squeedee/daisy-studio/sim/input/.!55486!Input-sim.asc

C5: cap
R11: res; 11k
R12: res; 1k
V_neg: voltage; 12
V_pos: voltage; 12
Named nets: +12V, 0, -12V, n+, n-, V_COM, IN_after_rcvr, Opamp_Out, Seed_In, Codec, IN_after_rcvr_Hot, Opamp_Out_Hot, Seed_In_Hot, n+_Hot, n-_Hot, Codec_Hot
