squeedee/daisy-studio/sim/input/amp-atten-bjt-tolerance.asc

C1: cap; 4.7µ
C2: cap; 20pF
C5: cap; {pcref}
C6: cap; {ncref}
C_aa: cap; 1n
D1: diode; RED_LED
Q1: pnp; 2N3906
Q2: npn; 2N3904
R1: res; {r1}
R2: res; {r2}
R3: res; 3k3
R4: res; 3k6
R5: res; 10k
R11: res; {pr1}
R12: res; {pr2}
R13: res; {nr2}
R14: res; {nr1}
R_led: res; 1k
R_pb: Res; {rpb}
R_pt: Res; {rpt}
U1: UniversalOpAmp2; Avol=1Meg GBW=53Meg Slew=24Meg Vhigh={vhi} Vlow={vlo}
U2: UniversalOpAmp2
V1: voltage; SINE(0 {vin} 1000); AC 1
V_COM: voltage; 2.5
V_neg: voltage; {v_rail}
V_pos: voltage; {v_rail}
V_thresh: voltage; 1
Named nets: +12V, 0, -12V, n+, n-, V_COM, IN_after_rcvr, Seed_In, Codec, Wiper
; settle for 3 seconds, 100ms of samples
.tran 0 3 2.9 1u
.model 2N3904 NPN(IS=6.734f BF=416.4 NF=1.259 VAF=74.03 IKF=66.78m ISE=6.734f NE=1.259 BR=0.7389 NR=2 VAR=28 IKR=0 ISC=0 NC=2 RB=10 RC=1 CJE=3.638p VJE=0.65 MJE=0.3085 TF=301.2p CJC=4.493p VJC=0.3742 MJC=0.2957 FC=0.5 TR=239.5n)
.model 2N3906 PNP(IS=1.41f BF=172.1 NF=1.232 VAF=115.7 IKF=30m ISE=1.41f NE=1.232 BR=3.72 NR=1.5 VAR=28 IKR=0 ISC=0 NC=2 RB=10 RC=1 CJE=4.5p VJE=0.65 MJE=0.28 TF=600p CJC=3.4p VJC=0.65 MJC=0.26 FC=0.5 TR=48n)
.model RED_LED D(IS=9.6e-18 N=2 RS=5.6 BV=5 IBV=10u EG=1.95)
Signal level after THAT 1246 (-6dB); 8.68V amp = +24 dBu balanced peak
BJT Clamp (2N3906/2N3904, ref dividers)
;Tolerance sweep: 5 corners x 3 testcases = 15 runs
;corner 1=TYP, 2=OPA_CLIP (max gain, min rails)
;        3=CLAMP_TIGHT (min V_ref, min rails)
;        4=CLAMP_LOOSE (max V_ref, max rails)
;        5=GAIN_LOW (min gain)
;testcase 1=+4dBu pk=1.0  (nominal pro, max pot)
;         2=+24dBu pk=0.26 (hot signal, full-scale)
;         3=+24dBu pk=1.0  (hot signal, mis-set)
Seed L/R In
PCM3060 Load
Clamp Ref Dividers (10k/1.6k from +/-12V, 47uF)
.param corner=1
.param testcase=1
.param v_rail=table(corner,1,12,2,11.4,3,11.4,4,12.6,5,12)
.param vhi=v_rail-1
.param vlo=1-v_rail
.param r1=table(corner,1,10k,2,9.9k,3,10k,4,10k,5,10.1k)
.param r2=table(corner,1,12k,2,12.12k,3,12k,4,12k,5,11.88k)
.param pr1=table(corner,1,10k,2,10k,3,10.1k,4,9.9k,5,10k)
.param pr2=table(corner,1,1.5k,2,1.5k,3,1.485k,4,1.515k,5,1.5k)
.param nr1=table(corner,1,10k,2,10k,3,10.1k,4,9.9k,5,10k)
.param nr2=table(corner,1,1.5k,2,1.5k,3,1.485k,4,1.515k,5,1.5k)
.param pcref=47u
.param ncref=47u
.param pk=table(testcase,1,1.0,2,0.26,3,1.0)
.param vin=table(testcase,1,0.868,2,8.68,3,8.68)
.param rpt={10k*(1-pk)+1m}
.param rpb={10k*pk+1m}
.step param corner list 1 2 3 4 5
.step param testcase list 1 2 3
.four 1000 V(Codec)
.meas tran codec_pp pp V(Codec)
.meas tran codec_max max V(Codec)
.meas tran codec_min min V(Codec)
.meas tran seed_pp pp V(Seed_In)
.meas tran seed_max max V(Seed_In)
.meas tran seed_min min V(Seed_In)
Clip indicator comparator
V_thresh sets trip point: 1V threshold on Seed_In (trim pot range AGND to n+)
Input level pot (10k log, 3-term divider)
;R_pt = top half, R_pb = bottom half
;pk = wiper position (0=mute, 1=CW max)
C_aa anti-alias 1nF C0G
;forms LPF with R_out + wiper Z
