squeedee/daisy-studio/sim/input/thd-plus4db.asc

C1: cap; 4.7µ
C2: cap; 20pF
C5: cap; {pcref}
C6: cap; {ncref}
D1: diode; BAV99
D2: diode; BAV99
R1: res; 10k
R2: res; {rfb}
R3: res; 2k2
R4: res; 3k6
R5: res; 10k
R11: res; {pr1}
R12: res; {pr2}
R13: res; {nr2}
R14: res; {nr1}
U1: UniversalOpAmp2; Avol=1Meg GBW=53Meg Slew=24Meg
V1: voltage; SINE(0 0.868 1000); AC 1
V_COM: voltage; 2.5
V_neg: voltage; 12
V_pos: voltage; 12
Named nets: +12V, 0, -12V, n+, n-, V_COM, IN_after_rcvr, Opamp_Out, Seed_In, Codec
; settle for 3 second, 100ms of samples
.tran 0 3 2.9 1u
.model BAV99 D(IS=3.18n RS=0.589 N=1.82 BV=70 IBV=100n CJO=1.15p M=0.35 TT=11.5n)
+4 dBu after THAT 1246 (-6dB)
Full gain at 25k
Symmetric Clamp (±2.45V ref)
Seed L/R In
PCM3060 Load
Clamp Ref Dividers (3k9/1k from ±12V, 470µF)
.param pr1=10k
.param pr2=1k
.param nr1=10k
.param nr2=1k
.param pcref=470u
.param ncref=470u
; .step param rfb 17k 19k 100
.param rfb=18.3k
Sweep R_fb (feedback resistor) from 15k to 25k in 500 ohm steps
; to find THD vs gain at +4dBu input
.four 1000 V(Codec)
.meas tran codec_pp pp V(Codec)
.meas tran seed_pp pp V(Seed_In)
