squeedee/daisy-studio/sim/output/gain-controlled-output.asc

D1: diode; 1N4004
D2: diode; 1N4004
D3: diode; 1N4004
D4: diode; 1N4004
E_cold: bv; V=if(-V(OPA_Out)>10.5,10.5,if(-V(OPA_Out)<-10.5,-10.5,-V(OPA_Out)))
E_hot: bv; V=if(V(OPA_Out)>10.5,10.5,if(V(OPA_Out)<-10.5,-10.5,V(OPA_Out)))
R_fb: res; {rfb}
R_in: res; {rin}
R_load: res; 10k
R_src: res; 100
U_opa: UniversalOpAmp2; Avol=1Meg GBW=53Meg Slew=24Meg Vhigh=11 Vlow=-11
V_neg: voltage; 12
V_pos: voltage; 12
V_sig: voltage; SINE(0 {vamp} 1000); AC 1
Named nets: +12V, 0, -12V, OPA_Out, XLR_Hot, XLR_Cold, Seed_Out
Gain-Controlled Balanced Output (Rev 2, sim/output/gain-controlled-output.asc)
Seed audio out -> OPA1656 inverting gain -> THAT1646 emulation -> XLR w/ phantom clamps
Seed full-scale: 2Vpp sine (1V amplitude), 100R source
OPA1656 inverting stage
;gain = -R_fb/R_in
;Vhigh/Vlow set rail clip
;at +/-11V (OPA1656 RRO)
THAT1646 emulation (behavioural):
;E_hot  = LIMIT(+V(OPA_Out), +/-10.5V)
;E_cold = LIMIT(-V(OPA_Out), +/-10.5V)
;Differential out = V(XLR_Hot) - V(XLR_Cold) = 2*V(OPA_Out) until clip
Phantom-power protection clamps (SM4004, modelled 1N4004).
;Each XLR pin clamped to +/-12V rails.
.param vamp=1
.param rin=2.2k
;uncomment to sweep gain and find clean ceiling:
;.step param rfb list 4.4k 6.6k 11k 13k 15k 22k 25k
.param rfb=18k
.tran 0 10m 5m 1u
.four 1000 V(XLR_Hot,XLR_Cold)
.meas tran opa_pp pp V(OPA_Out)
.meas tran opa_max max V(OPA_Out)
.meas tran opa_min min V(OPA_Out)
.meas tran hot_pp pp V(XLR_Hot)
.meas tran diff_pp pp V(XLR_Hot,XLR_Cold)
.meas tran diff_max max V(XLR_Hot,XLR_Cold)
.meas tran diff_min min V(XLR_Hot,XLR_Cold)
Expected: at rfb=13k (gain 5.9x) the OPA1656 output ~11.8Vpp,
;differential XLR ~23.6 Vpp = 8.3 Vrms = +20.6 dBu peak (clean).
;At rfb>=15k the OPA hits Vhigh/Vlow (+/-11V) -> clipped.
;At rfb=25k differential hits THAT1646 limit (2*10.5 = 21 Vpp).
.model 1N4004 D(Is=14.11n N=1.984 Rs=33.89m Ikf=94.81 Xti=3 Eg=1.11 Cjo=25.89p M=0.44 Vj=0.3245 Fc=0.5  Isr=1.565n Nr=2 Bv=400 Ibv=10u Tt=5.7u)
